TinyCircuits/TinyCircuits-Whisker-Accelerometer-AST1001/cad/Wireling_ACCELEROMETER_AST1001_REV1-DETAILED_DRAWING_COMPACT-PNG.png

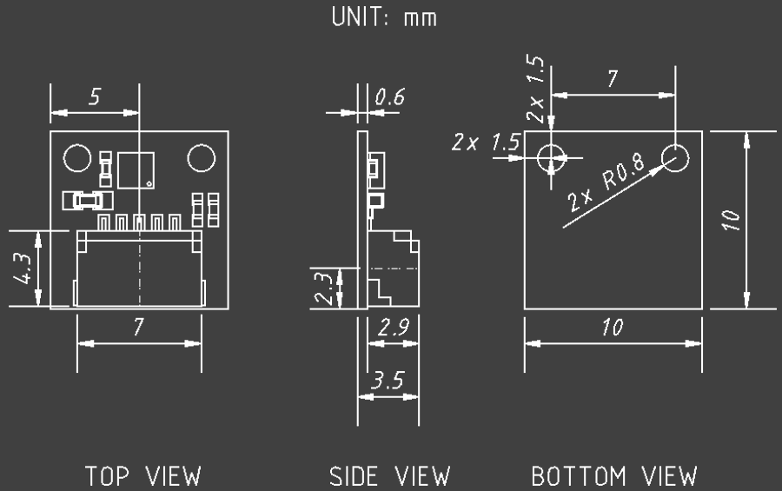
cad/Wireling_ACCELEROMETER_AST1001_REV1-DETAILED_DRAWING_COMPACT-PNG.png
