TinyCircuits/TinyCircuits-Whisker-Accelerometer-AST1001/images/AST1001-Tutorial-Image-03.png

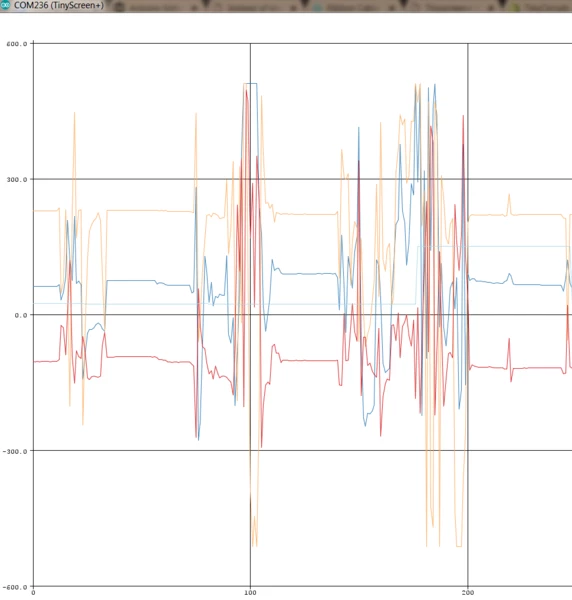
images/AST1001-Tutorial-Image-03.png
